nnayo/egere/elec/égère.sch

## KiCad design elec/égère.sch (2012-10-27)

Schematic: égère.sch

Parts:
C1: 0.1uF; SM1210L
D1: led alive (blue); LED-0805
D2: led take-off (red); LED-0805
K1: conn servo aero; 3_smd_pad
K2: conn servo cone; 3_smd_pad
K3: conn power arduino; 3_smd_pad
K4: conn sig arduino; 3_smd_pad
K5: conn switch open; 3_smd_pad
P1: main switch; 2_smd_pad
P2: Conn accu; 2_smd_pad
P3: conn MPU; 4_smd_pad
P4: conn num arduino; 4_smd_pad
R1, R2: 220; SM0805
U1: LM2937; SOT223

Notes on the sheet:
relay board
main switch
accu
servo aero
servo cone
open switch
arduino
MPU-6050
