nnayo/egere/soft/minut.h

#ifndef __MINUT_H__
# define __MINUT_H__


// ------------------------------------------
// public functions
//

// the task detecting the take-off and opening the parachute
extern void MNT_init(void);

extern void MNT_run(void);

#endif	// __MINUT_H__
